tdft/Stealthburner-CW2-Stealthburner-CW2-servo-cut-tip/jpg/1707468085880.png

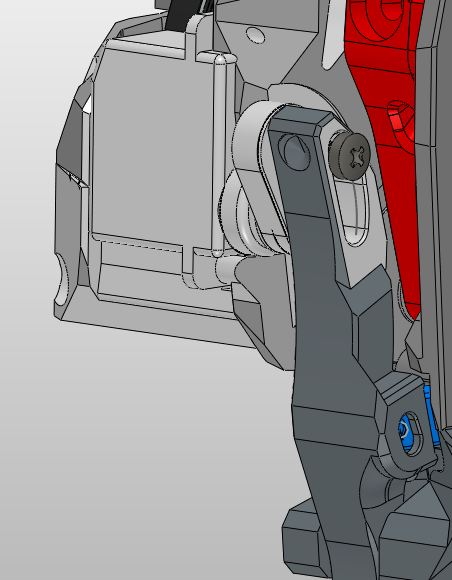
jpg/1707468085880.png
