tdft/Stealthburner-CW2-Stealthburner-CW2-servo-cut-tip/jpg/1707467149515.png

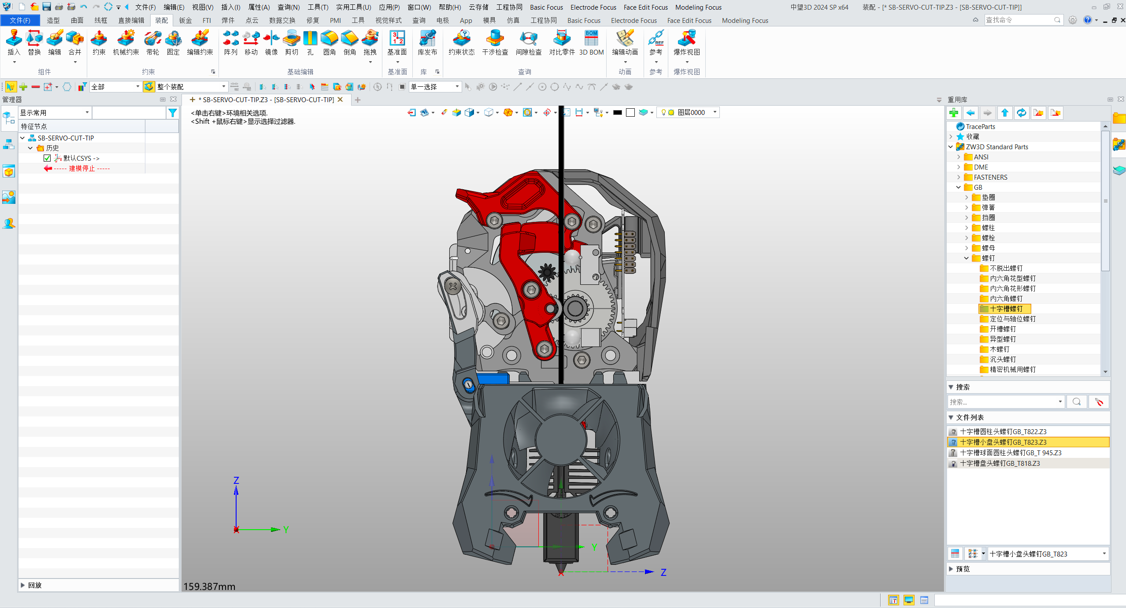
jpg/1707467149515.png
