tdft/Stealthburner-CW2-Stealthburner-CW2-servo-cut-tip/stls/根据热端打印/热端/Bambu/Bambu_Adapter.stl

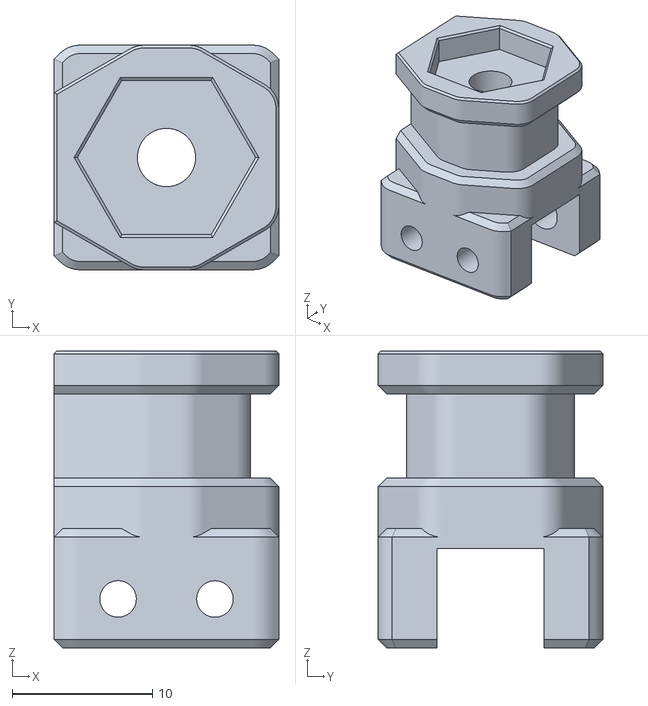
[picture p23: CAD file, 2024-03-18]
stls/根据热端打印/热端/Bambu/Bambu_Adapter.stl
16.0 x 16.0 x 21.2
