tdft/Stealthburner-CW2-Stealthburner-CW2-servo-cut-tip/stls/选打/sb2209无风扇.stl

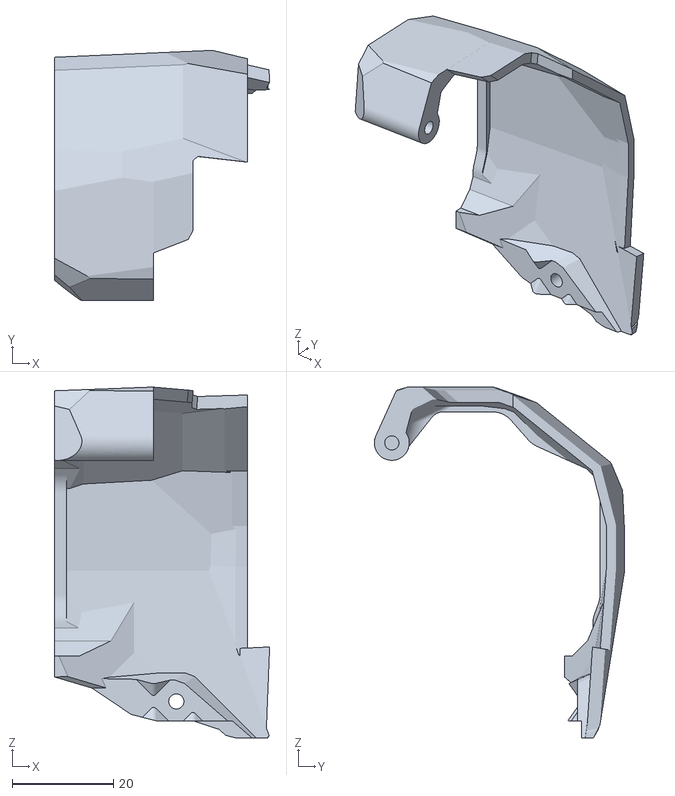
[picture p24: CAD file, 2024-03-18]
stls/选打/sb2209无风扇.stl
42.5 x 49.5 x 69.4
