tdft/Stealthburner-CW2-Stealthburner-CW2-servo-cut-tip/stls/选打/3.stl

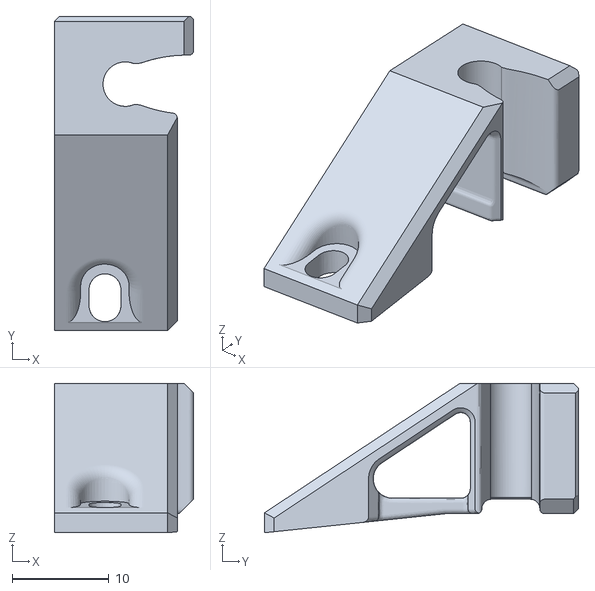
[picture p25: CAD file, 2024-03-18]
stls/选打/3.stl
14.4 x 32.5 x 15.5
